go4retro/CoCoMEMJr/media/IMG_8121.JPG

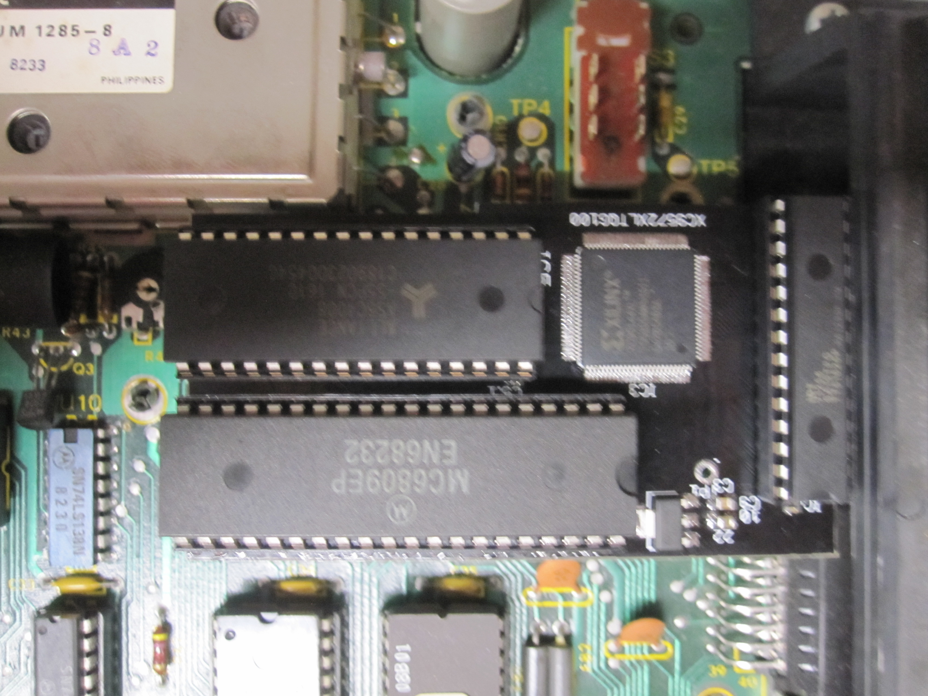
media/IMG_8121.JPG
