go4retro/CoCoMEMJr/media/IMG_8123.JPG

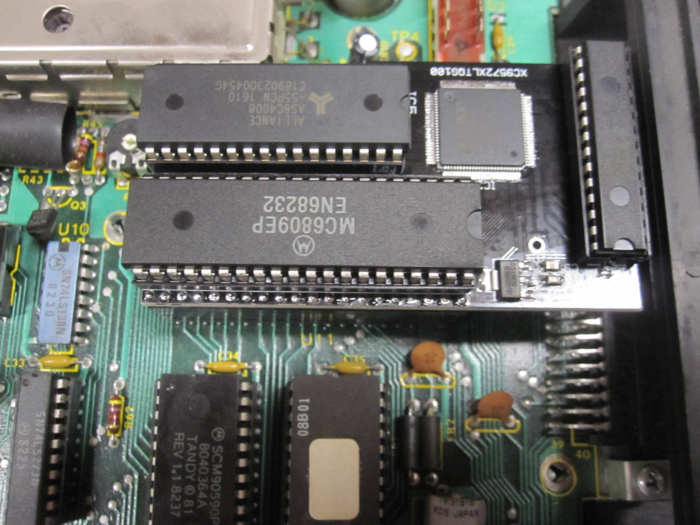
media/IMG_8123.JPG
