go4retro/CoCoMEMJr/media/IMG_8124 - Copy (Large).JPG

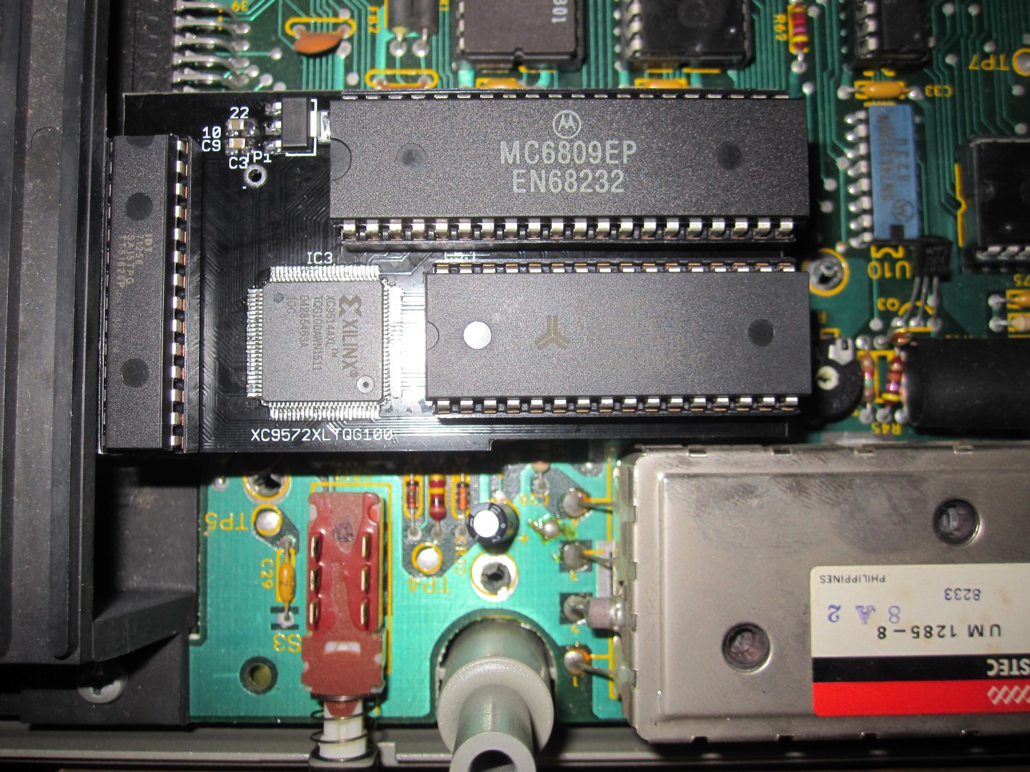
media/IMG_8124 - Copy (Large).JPG
