go4retro/CoCoMEMJr/media/IMG_8326.JPG

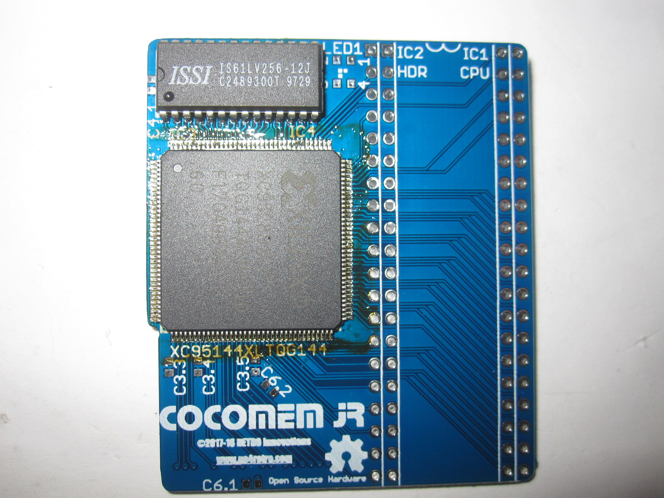
media/IMG_8326.JPG
