go4retro/CoCoMEMJr/media/IMG_8331.JPG

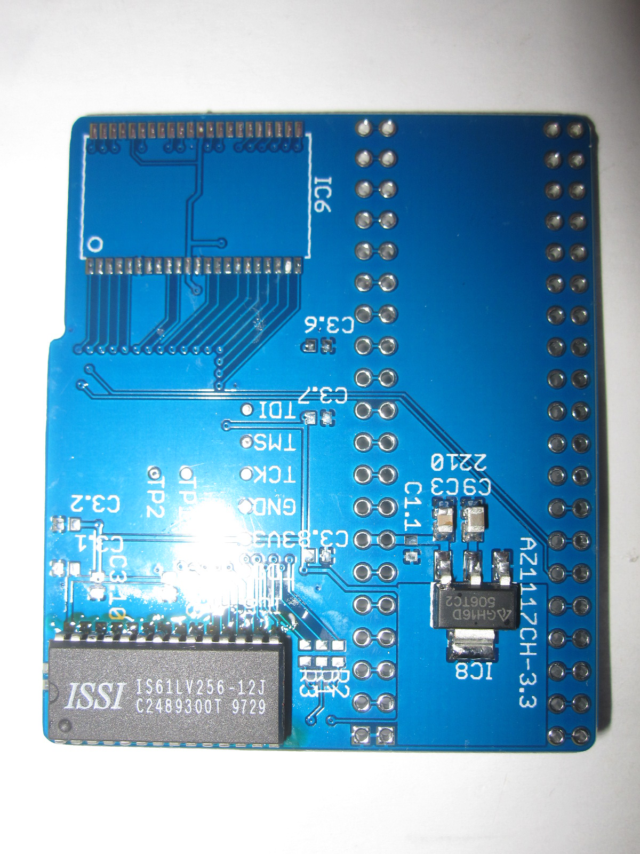
media/IMG_8331.JPG
