go4retro/CoCoMEMJr/media/IMG_8339.JPG

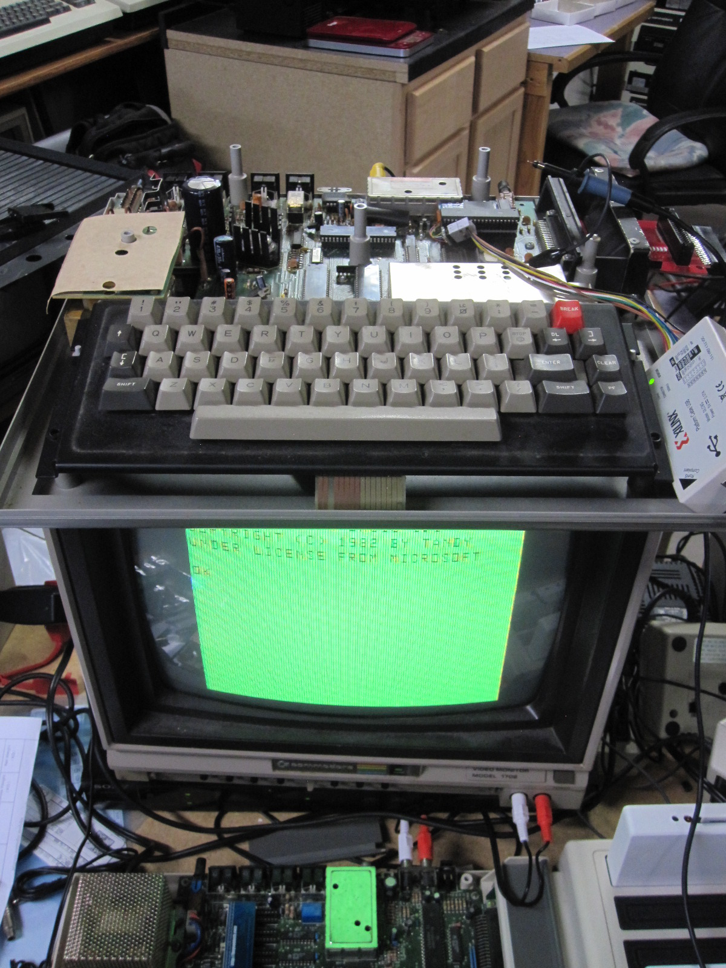
media/IMG_8339.JPG
