go4retro/CoCoMEMJr/media/IMG_8340.JPG

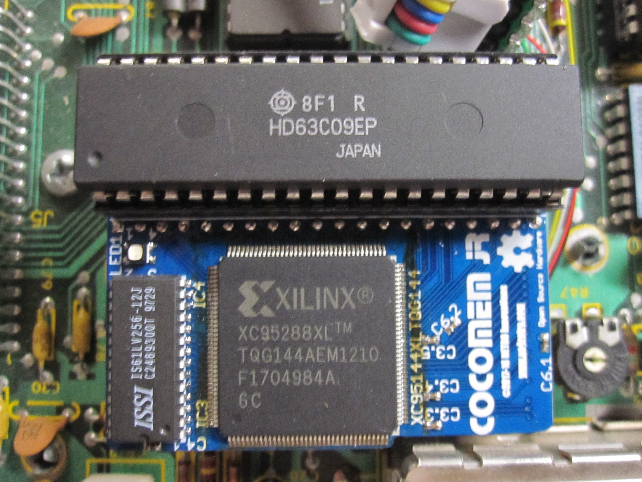
media/IMG_8340.JPG
