go4retro/CoCoMEMJr/pcb/CocoMemJr.bmp

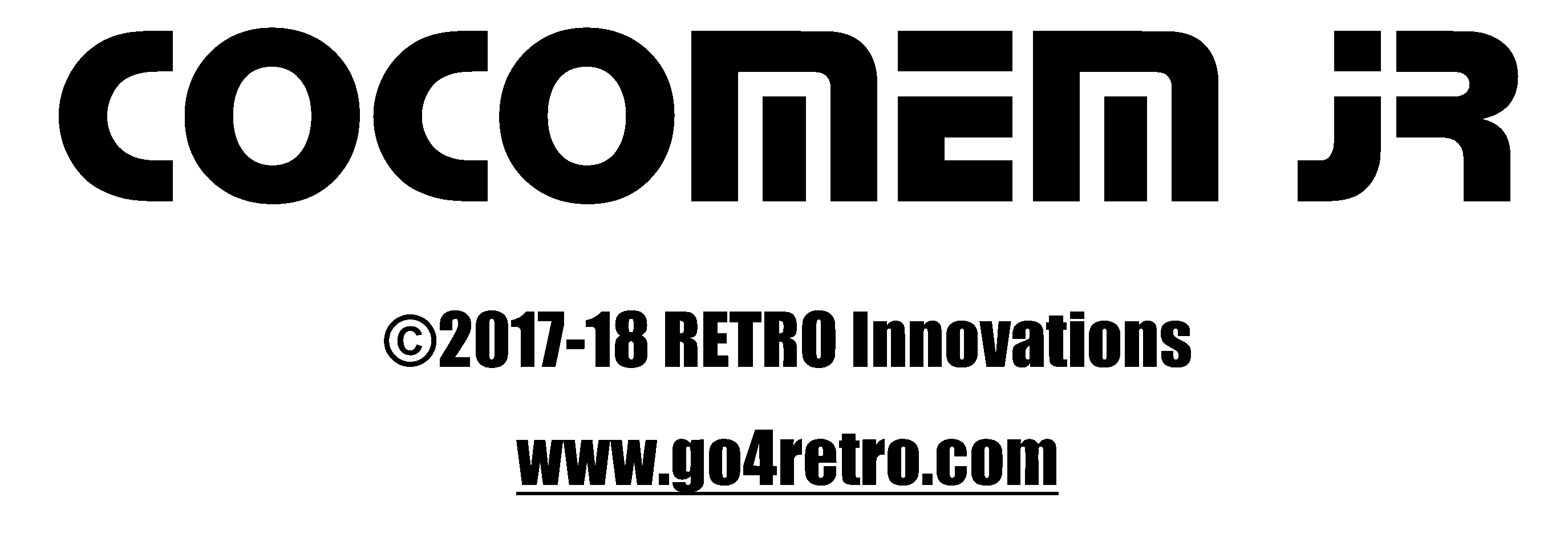
pcb/CocoMemJr.bmp
