go4retro/CoCoMEMJr/pcb/CocoMEMJr_v1.01 PCB.png

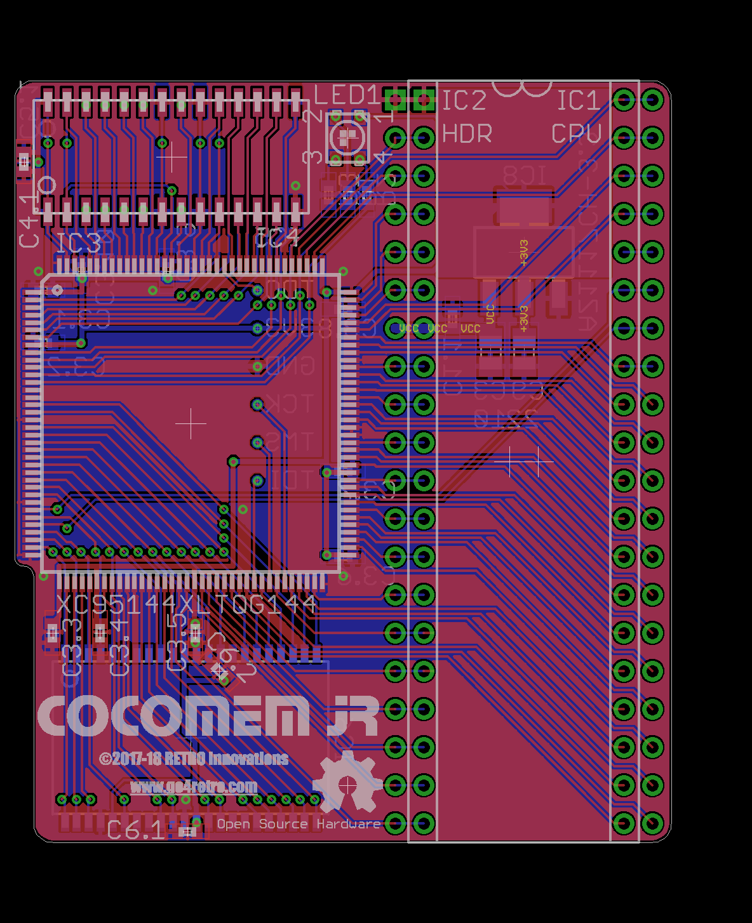
pcb/CocoMEMJr_v1.01 PCB.png
