go4retro/CoCoMEMJr/media/IMG_8124.JPG

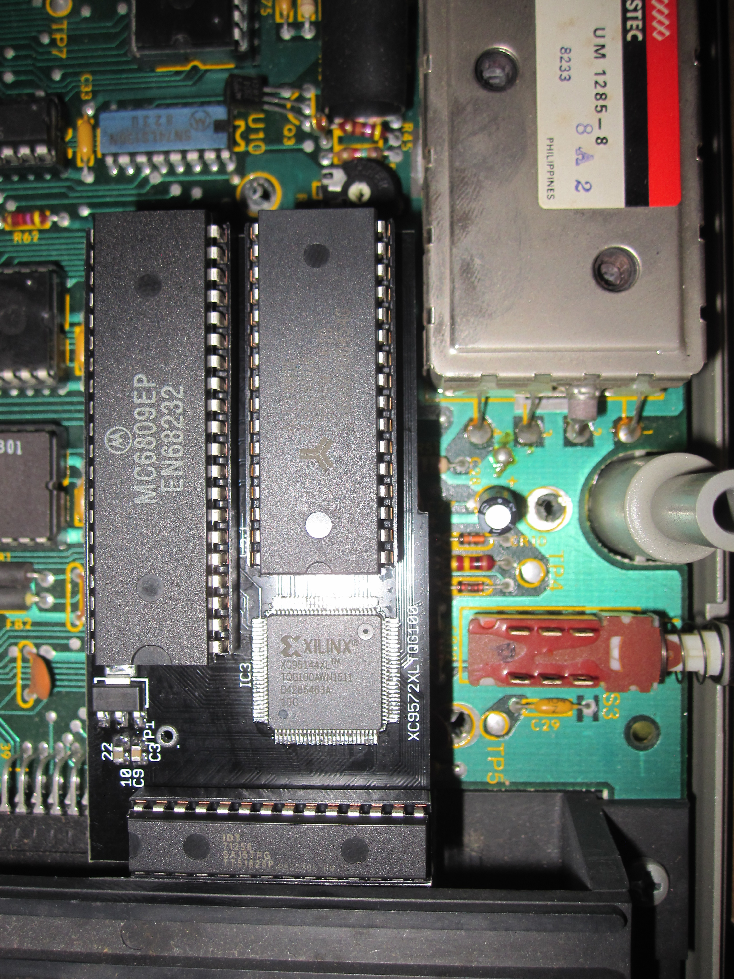
media/IMG_8124.JPG
